th0mpy/Voron0-2040-display/Images/IMG_1681.jpeg

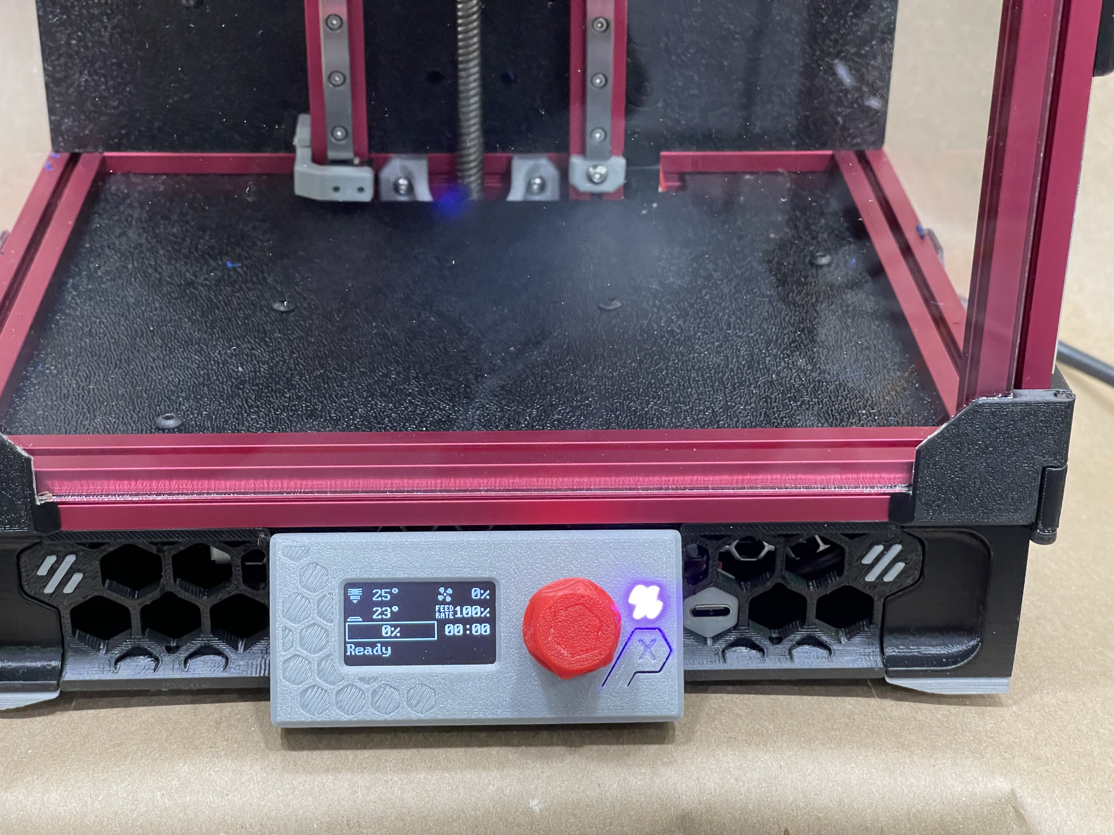
Images/IMG_1681.jpeg
